yuburoll/KeeNoard/images/encoderFront.jpg

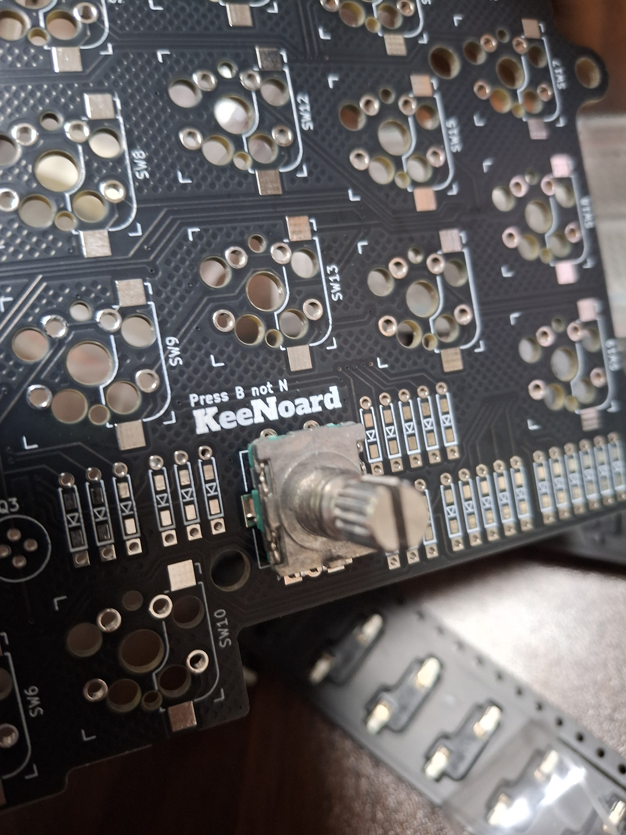
images/encoderFront.jpg
