yuburoll/KeeNoard/images/jumpers0.jpg

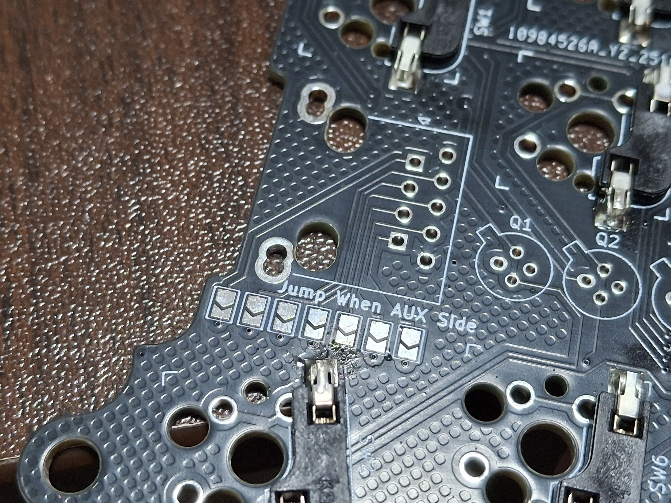
images/jumpers0.jpg
