yuburoll/KeeNoard/images/jumpers1.jpg

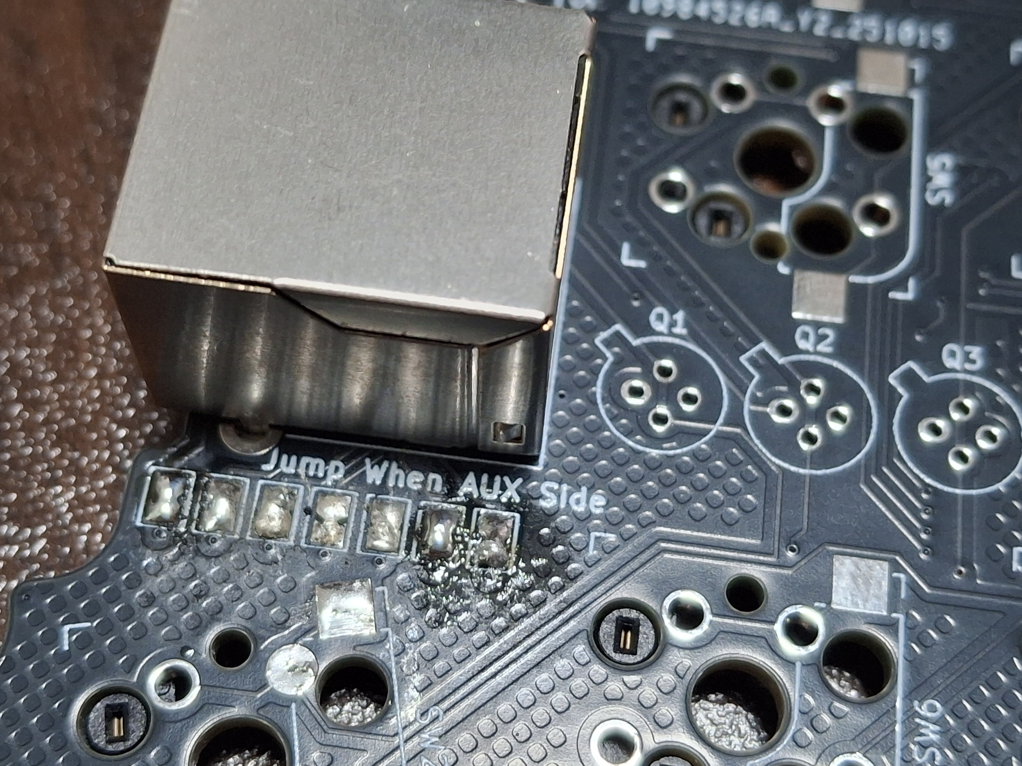
images/jumpers1.jpg
