yuburoll/KeeNoard/images/keenoardBoard.jpg

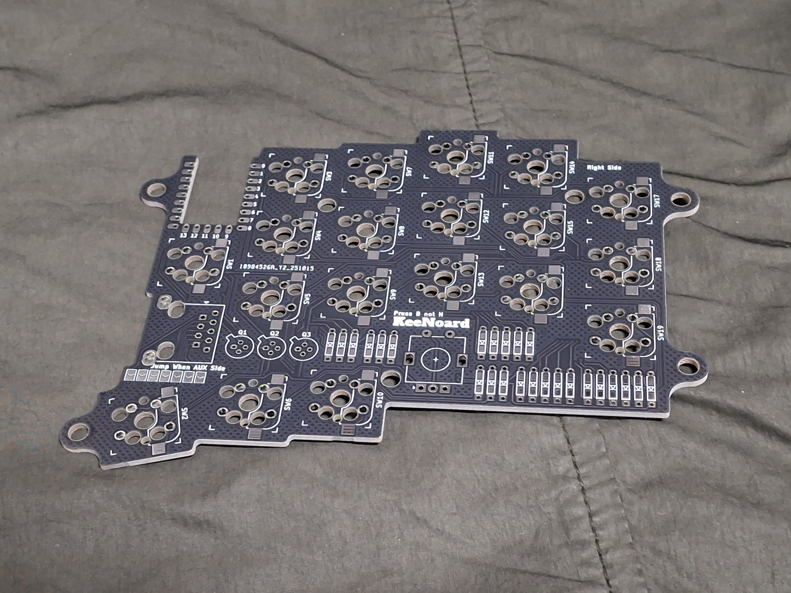
images/keenoardBoard.jpg
