yuburoll/KeeNoard/images/keenoardCaseV1.jpg

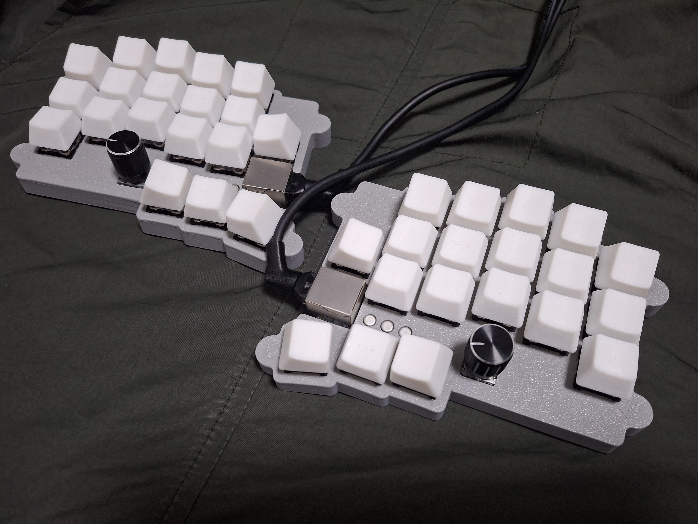
images/keenoardCaseV1.jpg
