yuburoll/KeeNoard/images/keenoardCaseV2.jpg

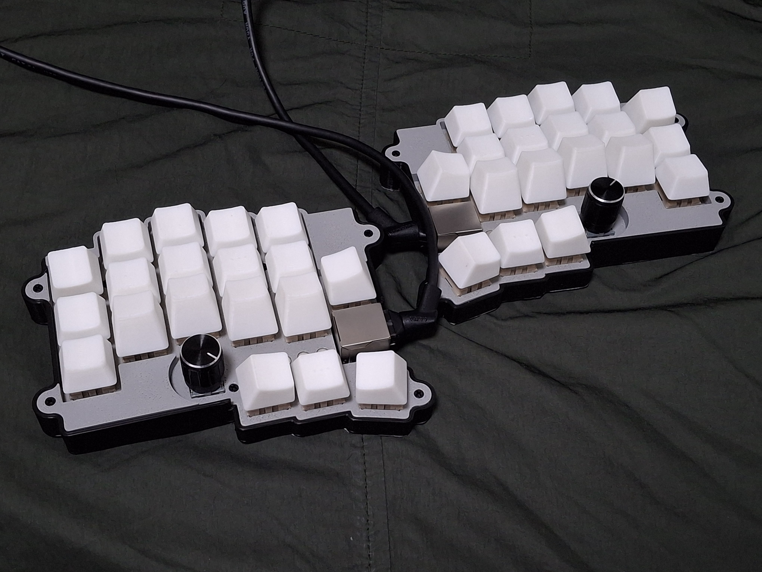
images/keenoardCaseV2.jpg
