yuburoll/KeeNoard/images/boardSolder0.jpg

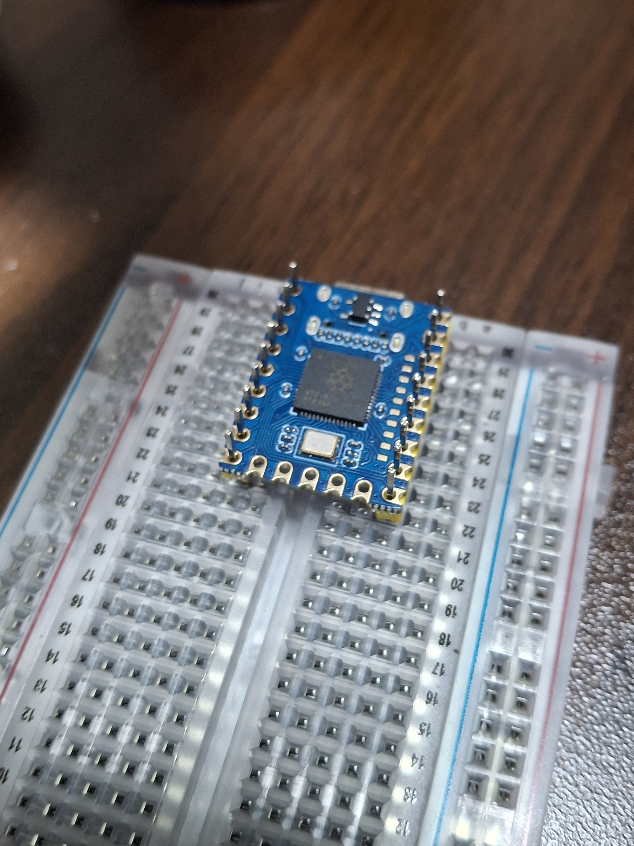
images/boardSolder0.jpg
