yuburoll/KeeNoard/images/boardSolder2.jpg

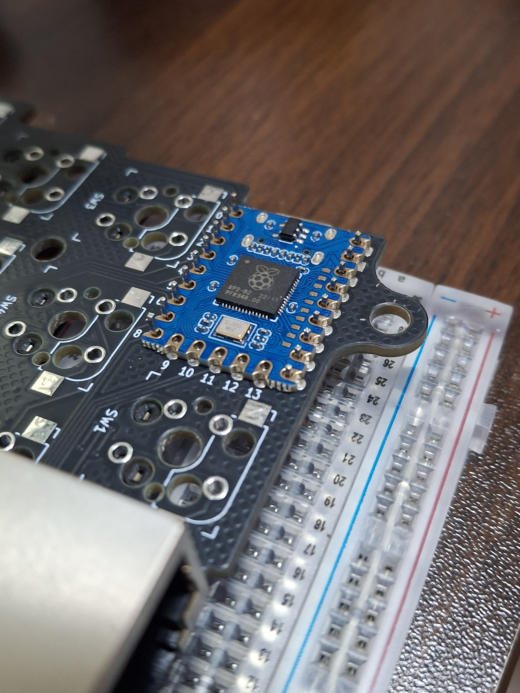
images/boardSolder2.jpg
