yuburoll/KeeNoard/images/caseV1Assembly0.jpg

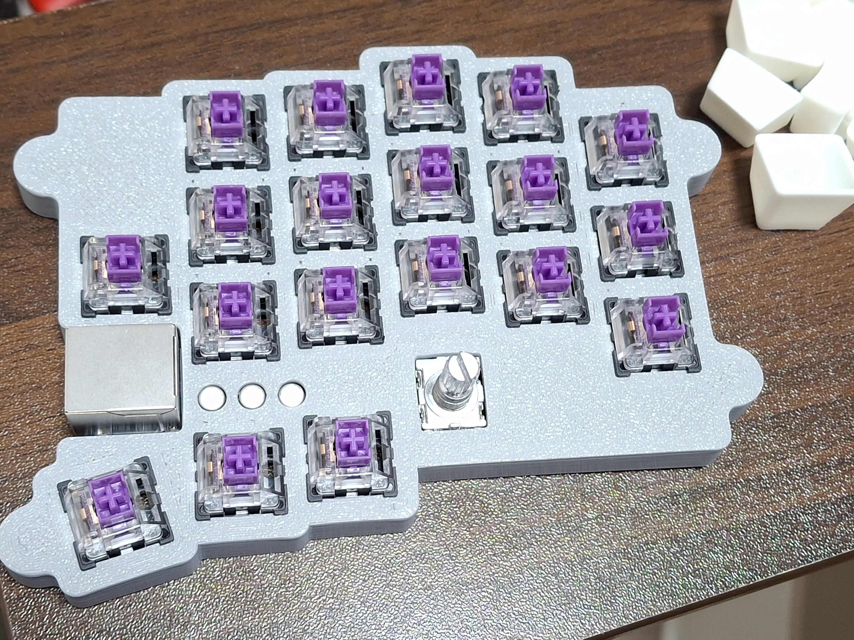
images/caseV1Assembly0.jpg
