yuburoll/KeeNoard/images/caseV1Assembly3.jpg

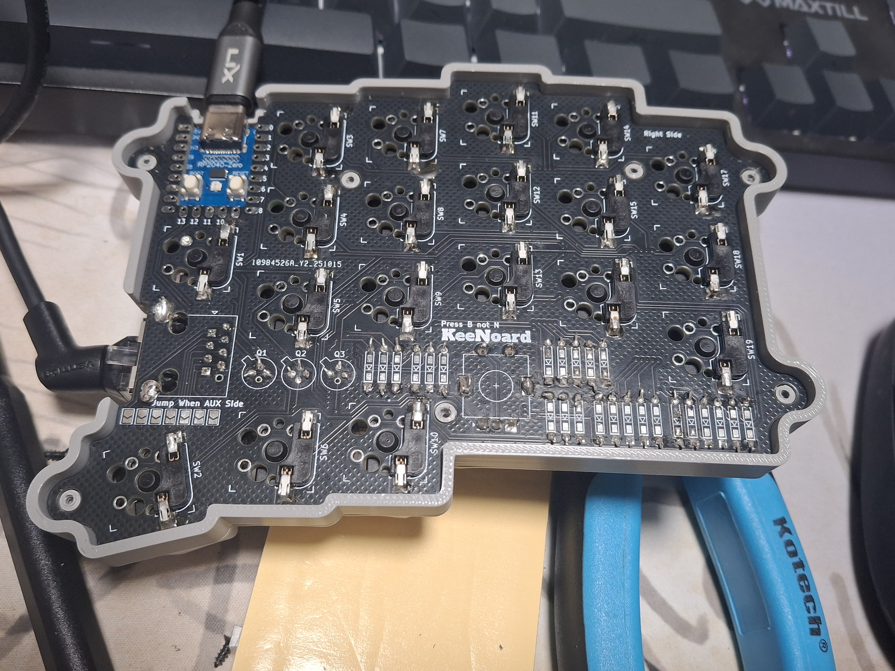
images/caseV1Assembly3.jpg
