yuburoll/KeeNoard/images/caseV2Assembly0.jpg

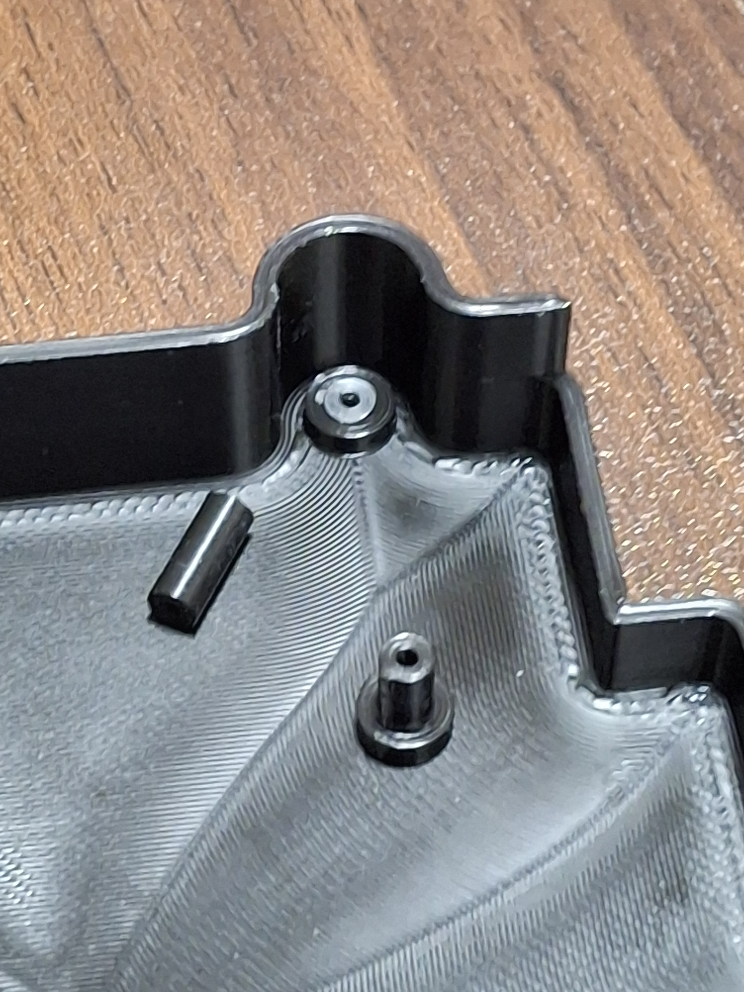
images/caseV2Assembly0.jpg
