yuburoll/KeeNoard/images/caseV2Assembly1.jpg

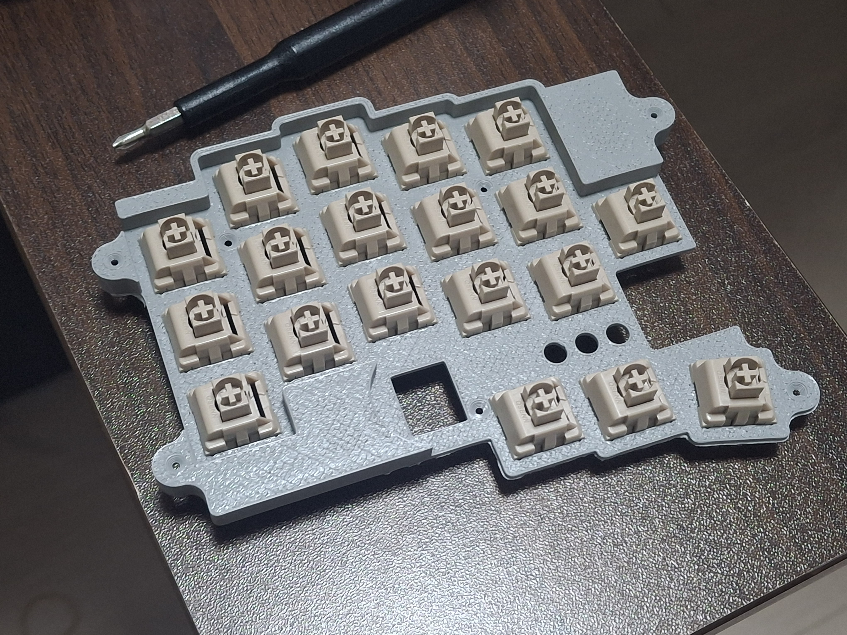
images/caseV2Assembly1.jpg
