yuburoll/KeeNoard/images/caseV2Assembly2.jpg

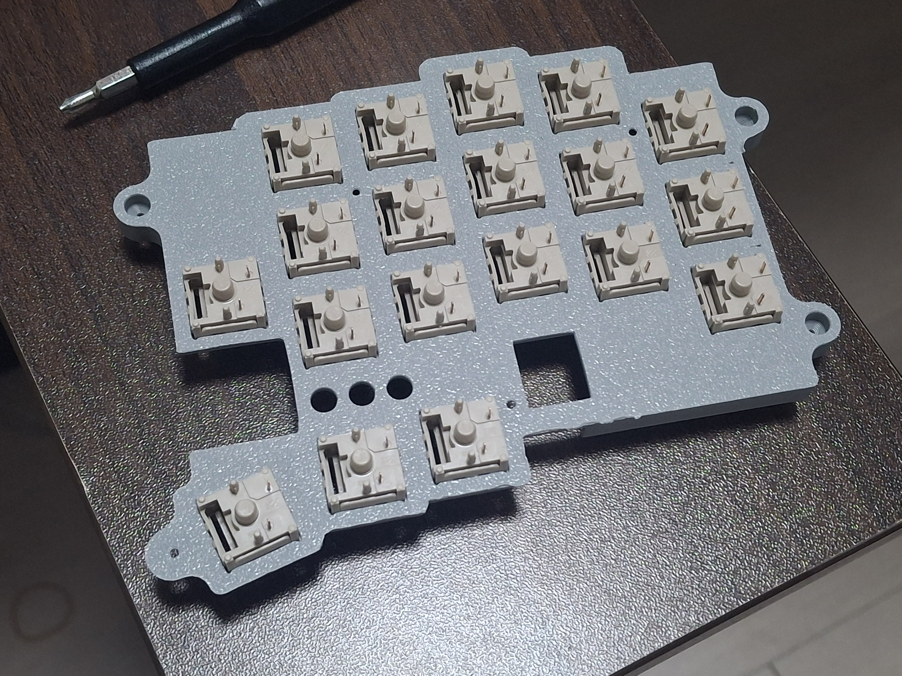
images/caseV2Assembly2.jpg
