yuburoll/KeeNoard/images/caseV2Assembly3.jpg

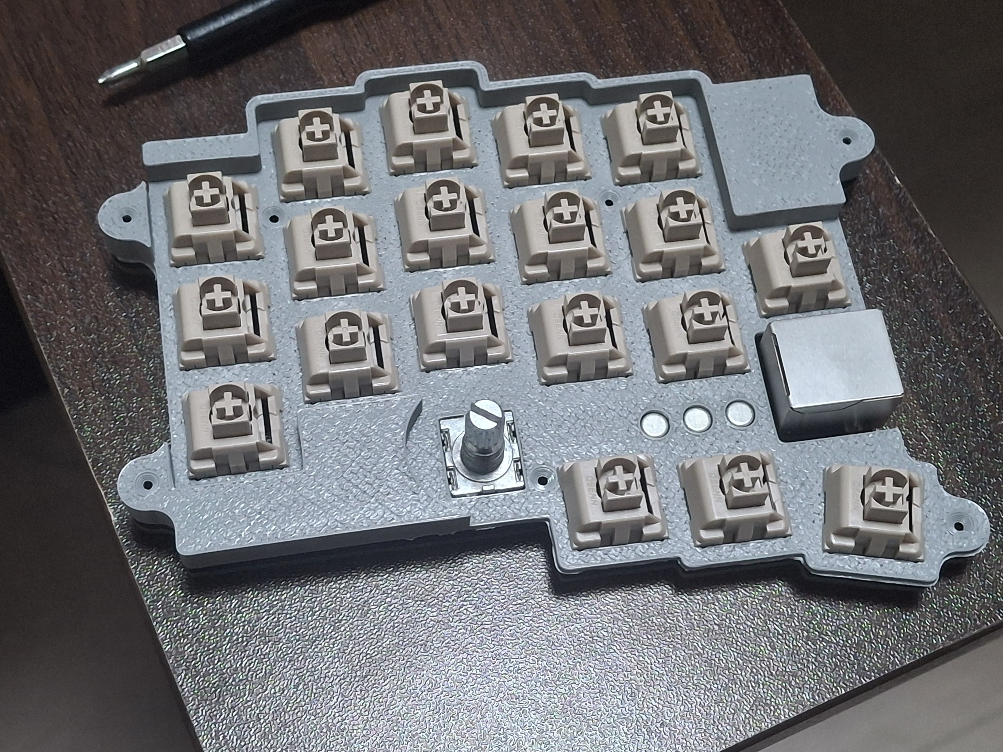
images/caseV2Assembly3.jpg
