yuburoll/KeeNoard/images/caseV2Assembly4.jpg

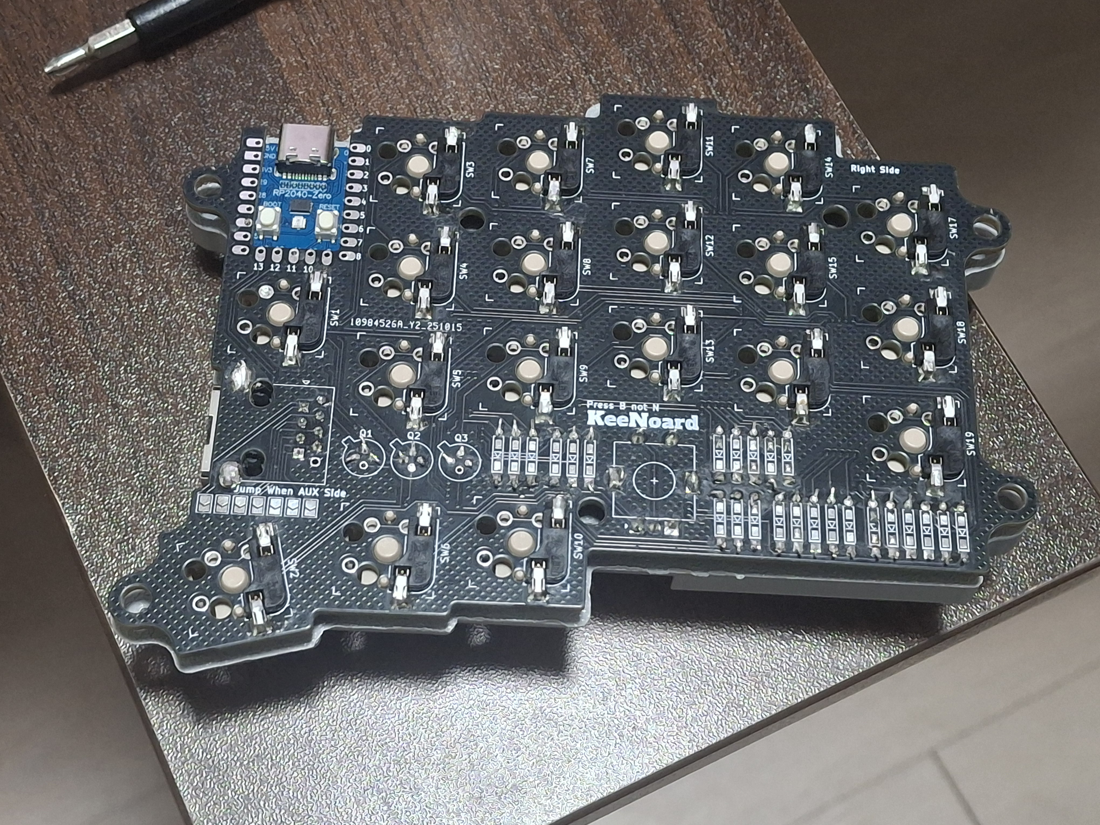
images/caseV2Assembly4.jpg
