yuburoll/KeeNoard/images/caseV2Assembly6.jpg

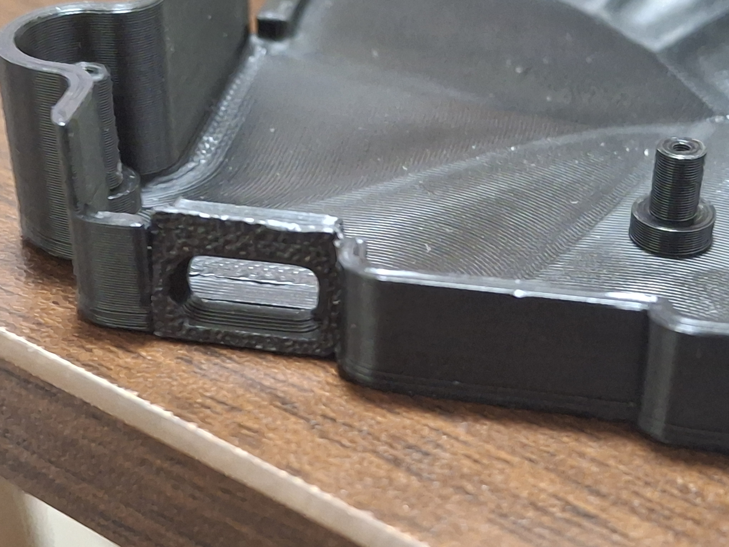
images/caseV2Assembly6.jpg
