yuburoll/KeeNoard/images/caseV2Assembly7.jpg

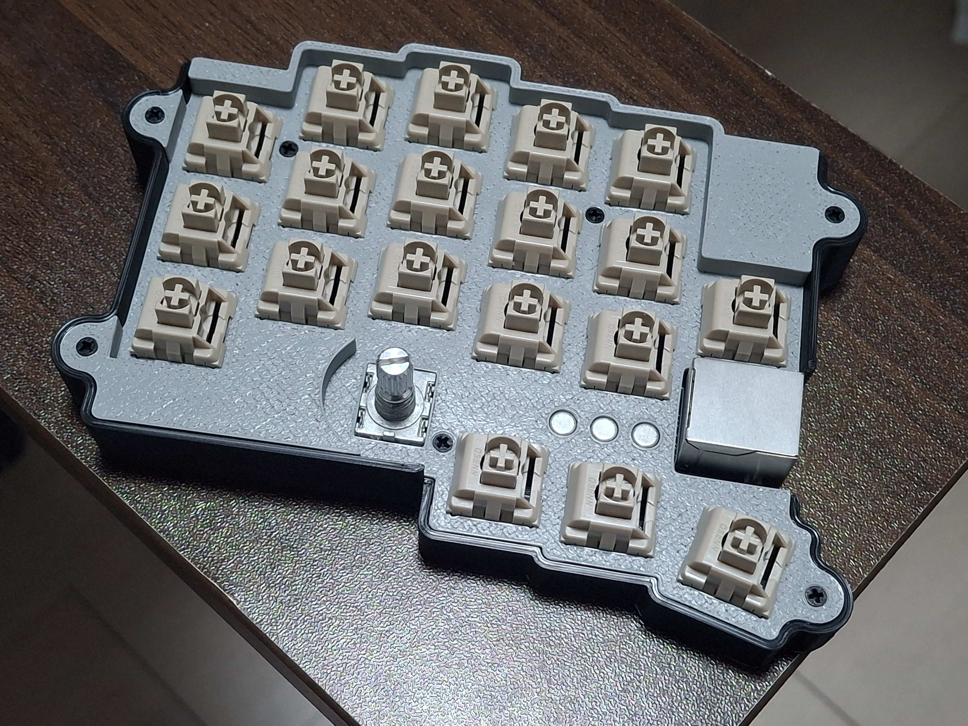
images/caseV2Assembly7.jpg
