yuburoll/KeeNoard/images/caseV2Assembly8.jpg

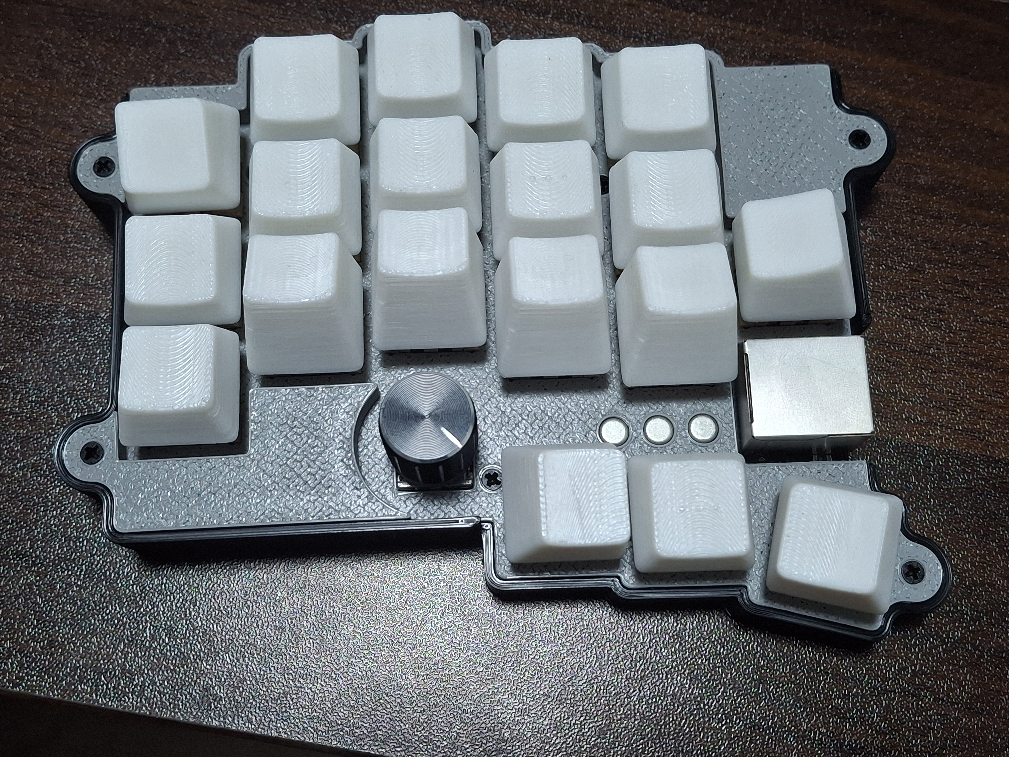
images/caseV2Assembly8.jpg
