yuburoll/KeeNoard/images/caseV3Assembly0.jpg

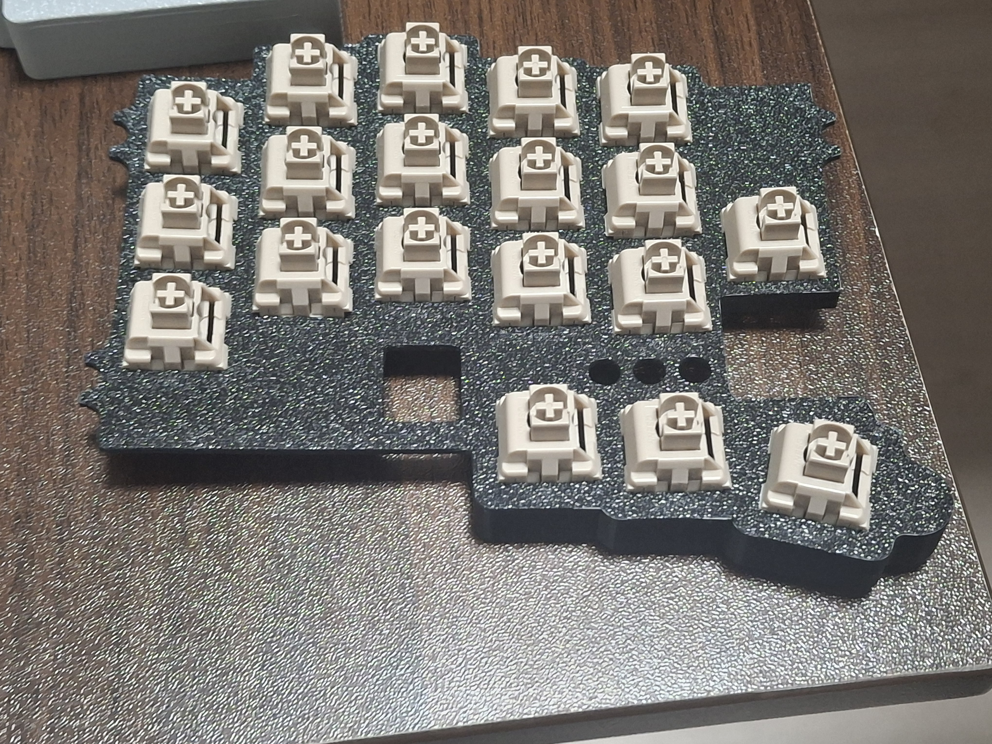
images/caseV3Assembly0.jpg
