yuburoll/KeeNoard/images/caseV3Assembly1.jpg

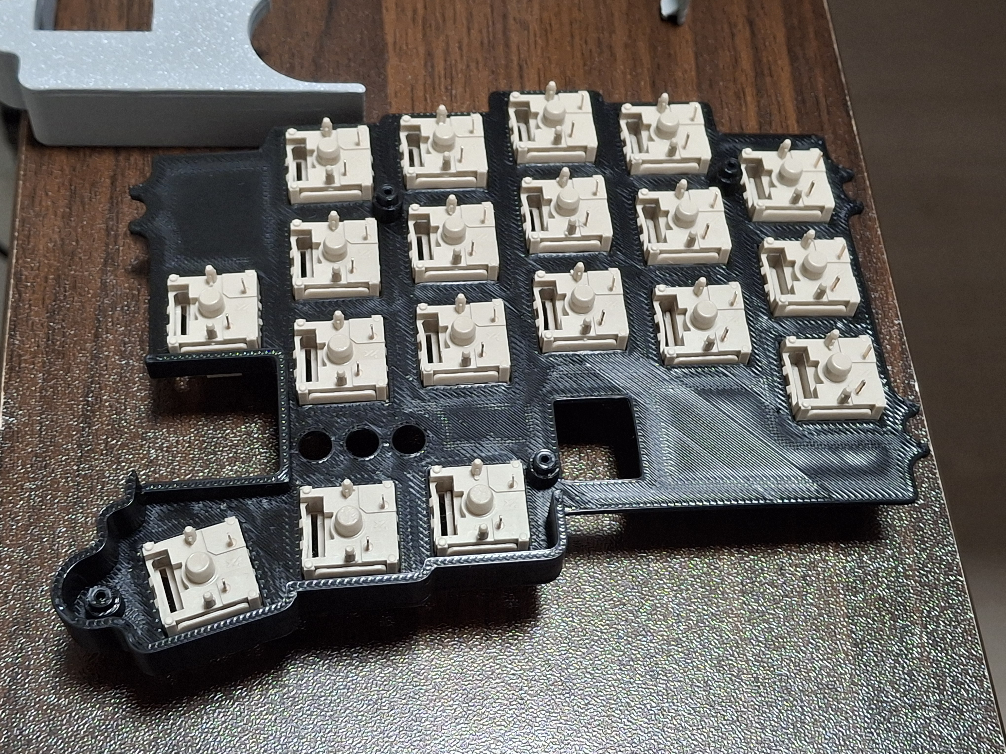
images/caseV3Assembly1.jpg
