yuburoll/KeeNoard/images/caseV3Assembly2.jpg

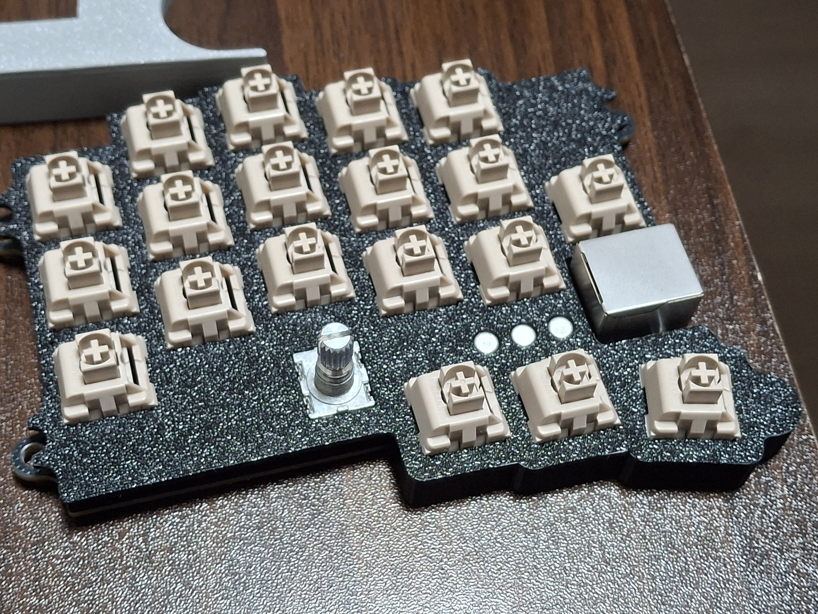
images/caseV3Assembly2.jpg
