yuburoll/KeeNoard/images/caseV3Assembly4.jpg

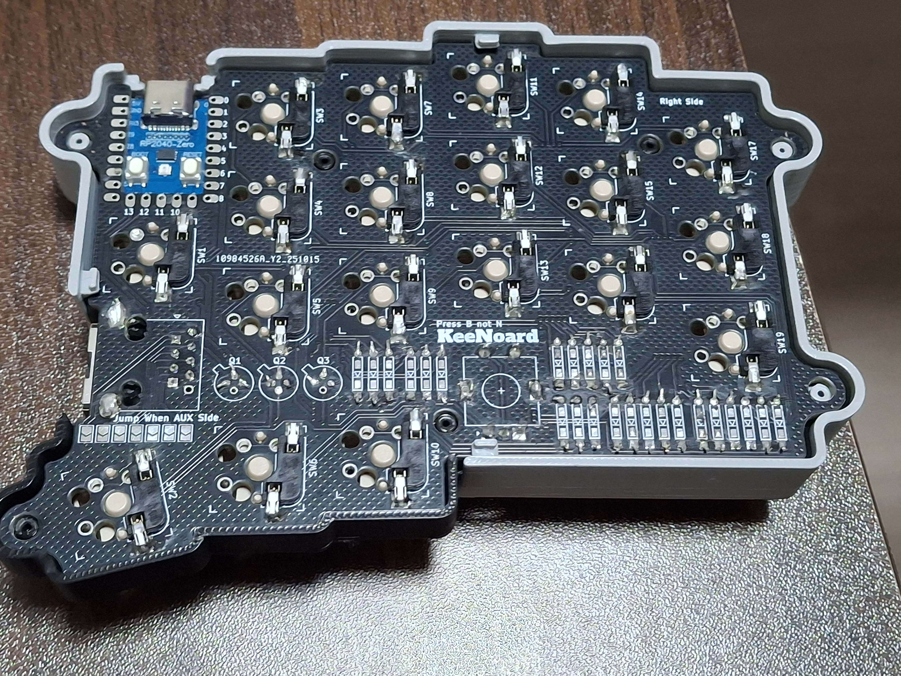
images/caseV3Assembly4.jpg
