yuburoll/KeeNoard/images/caseV3Assembly5.jpg

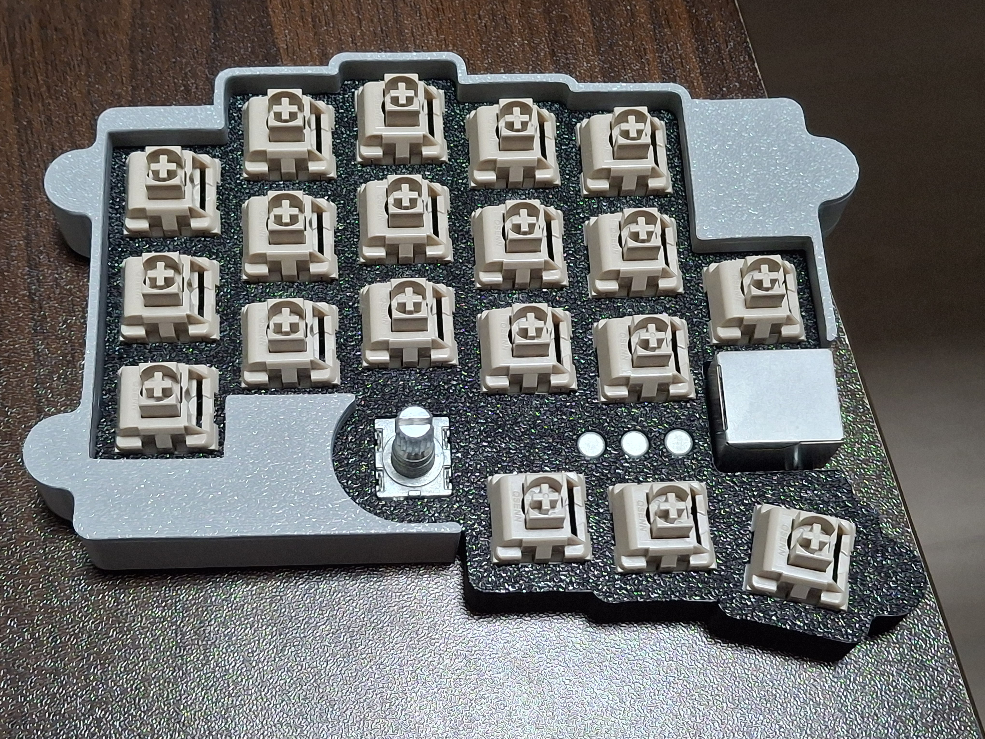
images/caseV3Assembly5.jpg
