yuburoll/KeeNoard/images/caseV3Assembly6.jpg

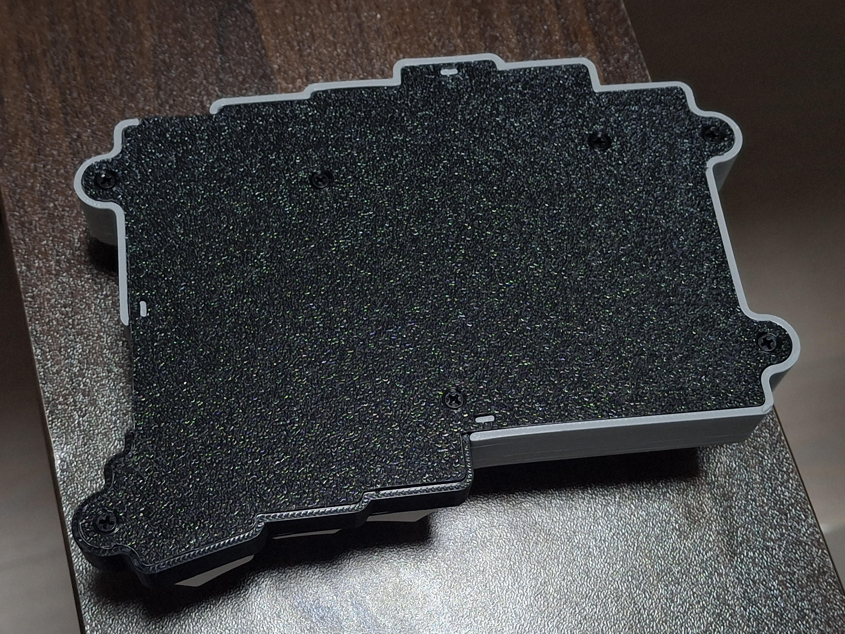
images/caseV3Assembly6.jpg
