yuburoll/KeeNoard/images/diodesSolder0.jpg

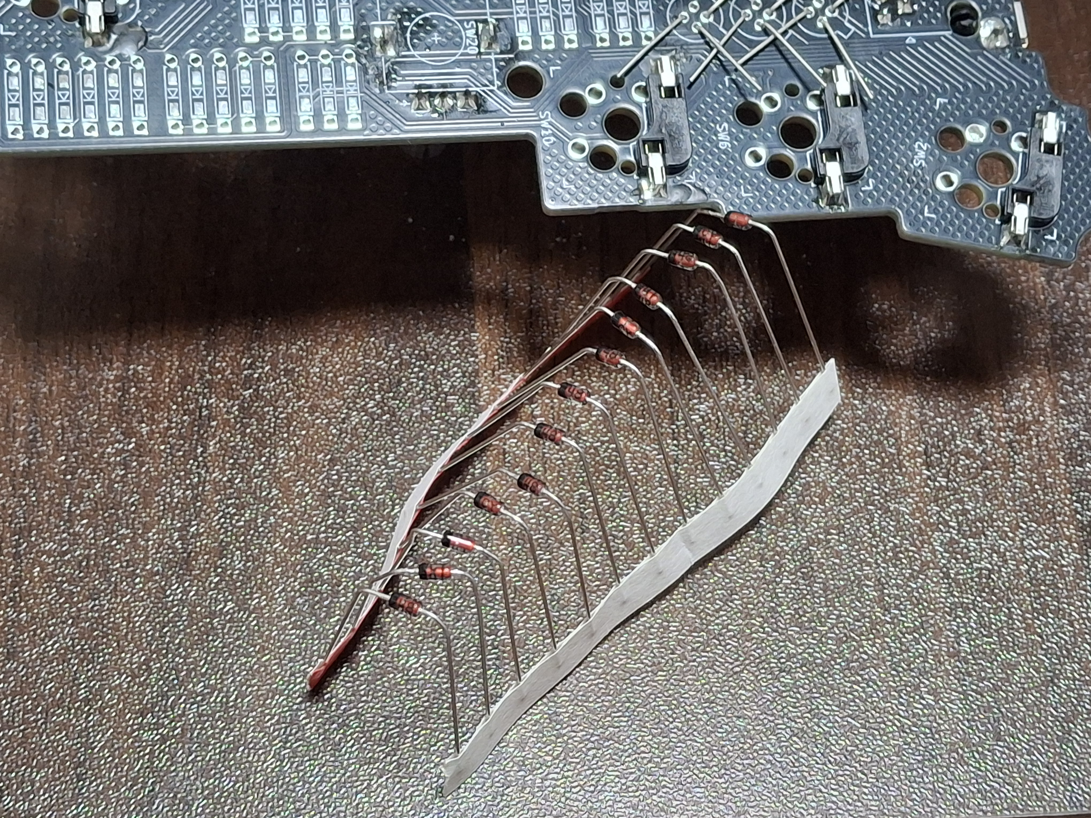
images/diodesSolder0.jpg
