yuburoll/KeeNoard/images/transistorSolder1.jpg

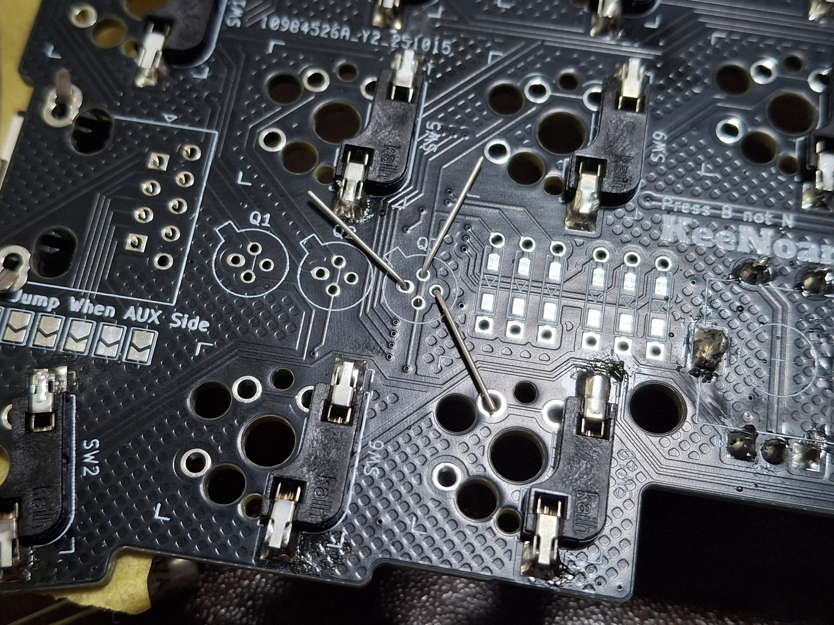
images/transistorSolder1.jpg
