yuburoll/KeeNoard/images/transistorSolder2.jpg

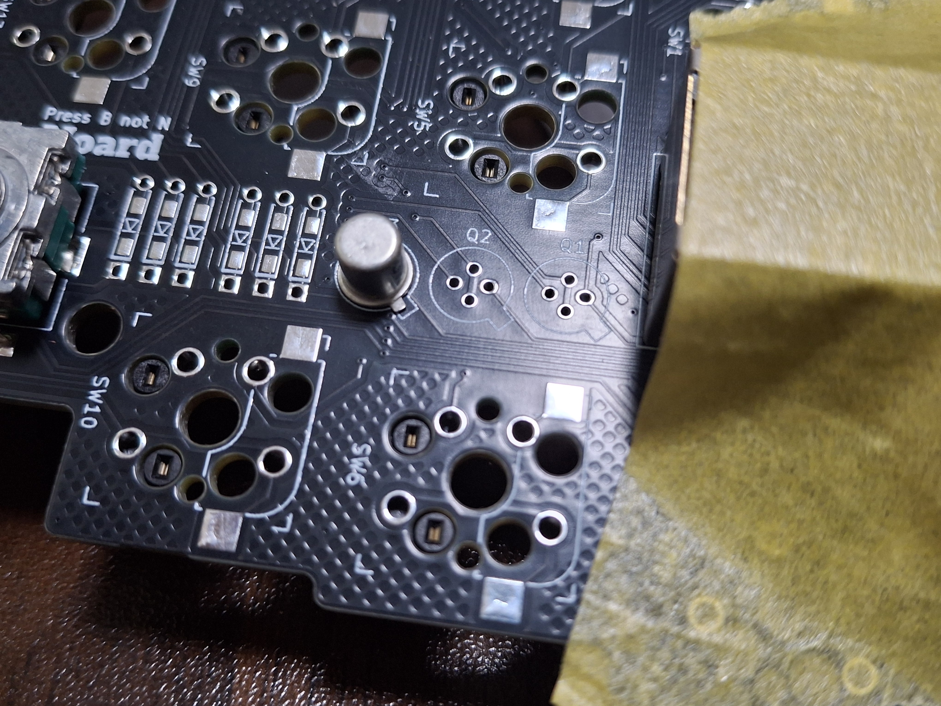
images/transistorSolder2.jpg
