yuburoll/KeeNoard/kicad/KeeNoard-SMD.kicad_sch

## KiCad design kicad/KeeNoard-SMD.kicad_sch (2025-10-31)

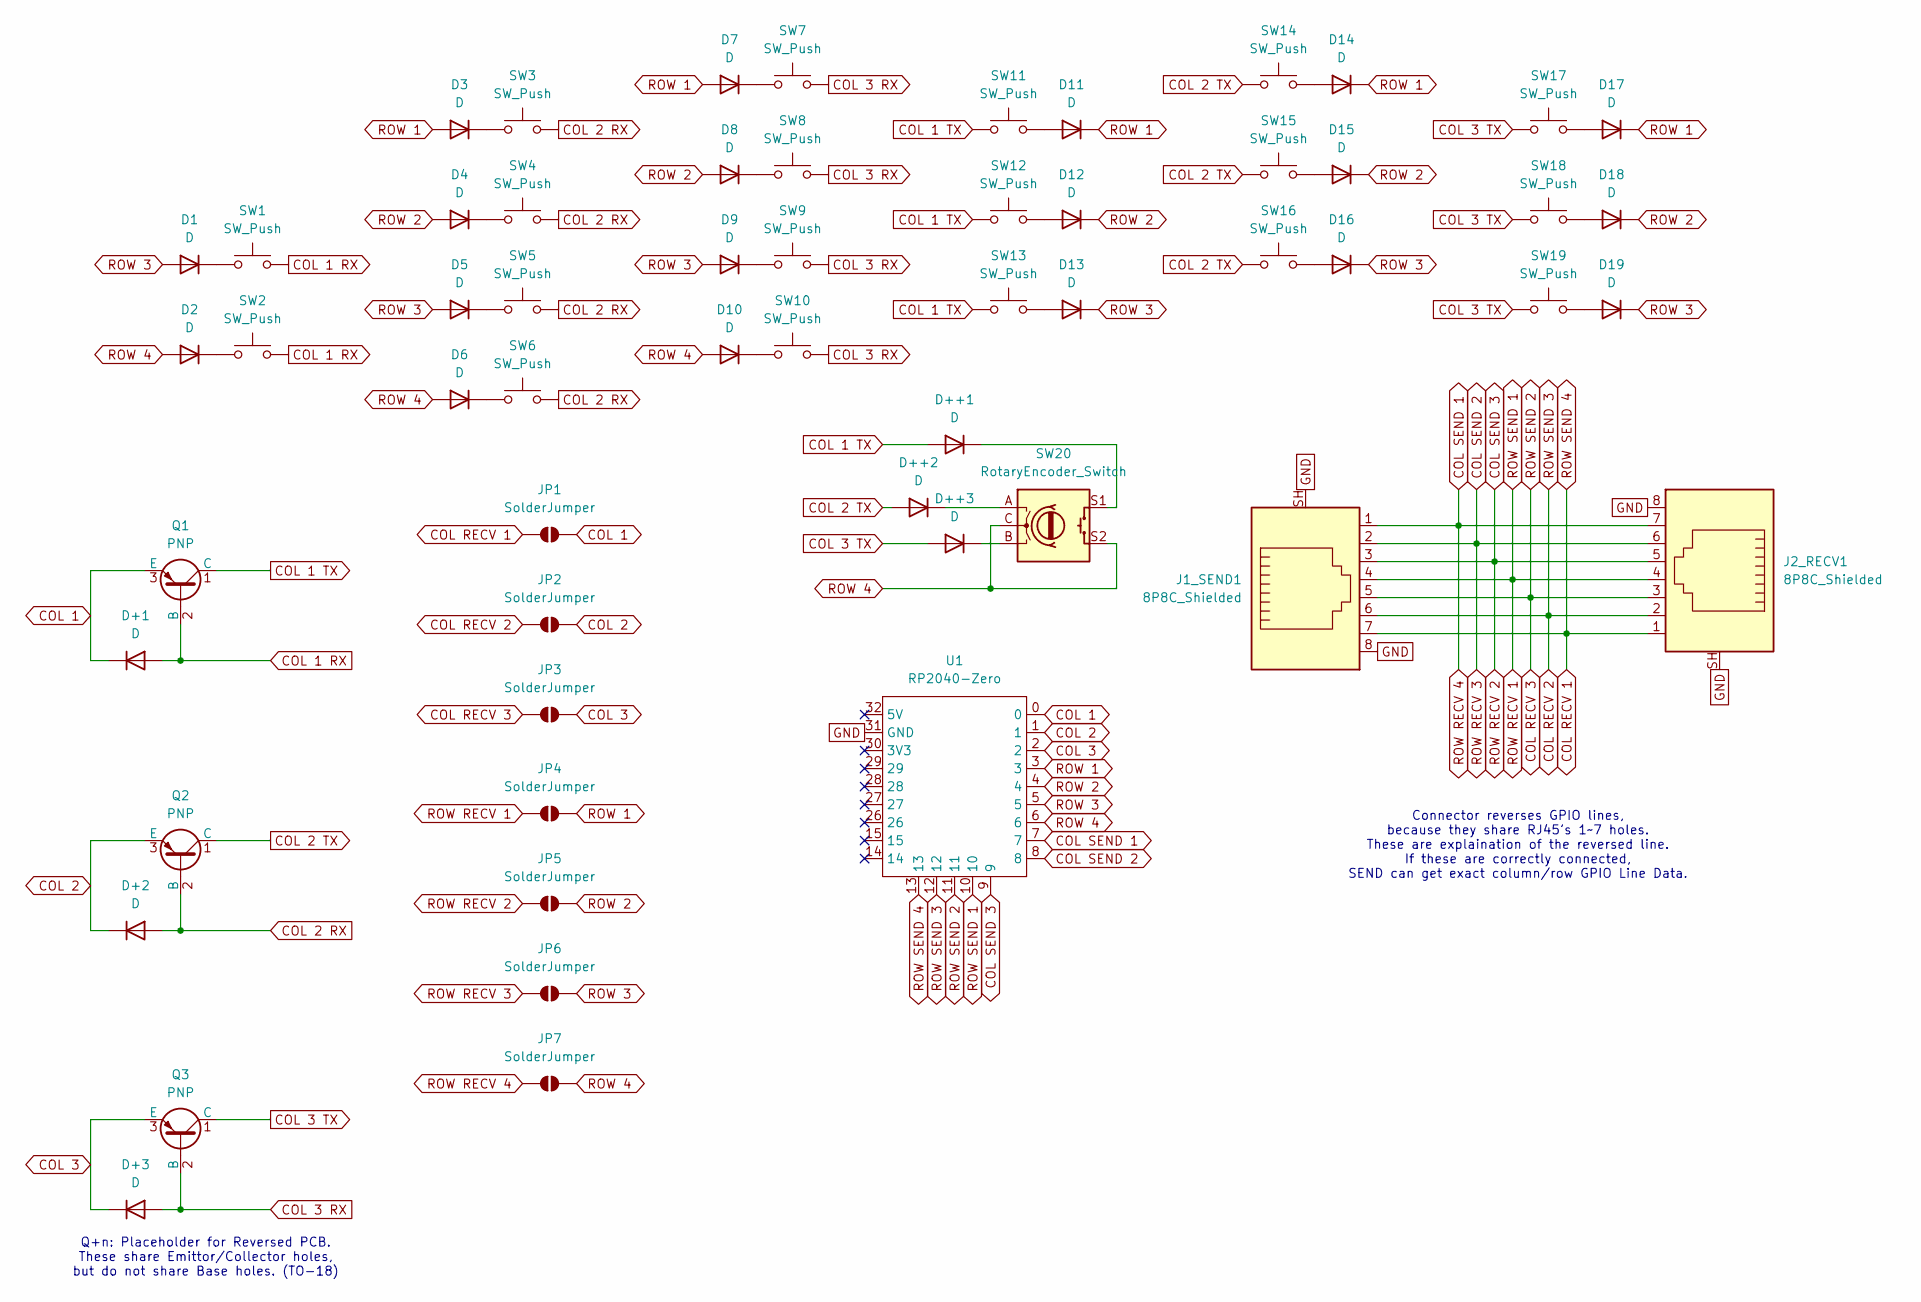
[picture p42: schematic KeeNoard-SMD.kicad_sch]

Parts:
D1, D2, D3, D4, D5, D6, D7, D8, D9, D10, D11, D12, D13, D14, D15, D16, D17, D18, D19: D
D+1, D+2, D+3: D
D++1, D++2, D++3: D
J1_SEND1, J2_RECV1: 8P8C_Shielded
JP1, JP2, JP3, JP4, JP5, JP6, JP7: SolderJumper
Q1, Q2, Q3: PNP
SW1, SW2, SW3, SW4, SW5, SW6, SW7, SW8, SW9, SW10, SW11, SW12, SW13, SW14, SW15, SW16, SW17, SW18, SW19: SW_Push
SW20: RotaryEncoder_Switch
U1: RP2040-Zero

Connections:
COL 1: D+1.1 (K), JP1.2 (B), Q1.3 (E), U1.0
COL 1 RX: D+1.2 (A), Q1.2 (B), SW1.1, SW2.1
COL 1 TX: D++1.2 (A), Q1.1 (C), SW11.2, SW12.2, SW13.2
COL 2: D+2.1 (K), JP2.2 (B), Q2.3 (E), U1.1
COL 2 RX: D+2.2 (A), Q2.2 (B), SW3.1, SW4.1, SW5.1, SW6.1
COL 2 TX: D++2.2 (A), Q2.1 (C), SW14.2, SW15.2, SW16.2
COL 3: D+3.1 (K), JP3.2 (B), Q3.3 (E), U1.2
COL 3 RX: D+3.2 (A), Q3.2 (B), SW7.1, SW8.1, SW9.1, SW10.1
COL 3 TX: D++3.2 (A), Q3.1 (C), SW17.2, SW18.2, SW19.2
COL RECV 1: J1_SEND1.7, J2_RECV1.1, JP1.1 (A), U1.13
COL RECV 2: J1_SEND1.6, J2_RECV1.2, JP2.1 (A), U1.12
COL RECV 3: J1_SEND1.5, J2_RECV1.3, JP3.1 (A), U1.11
COL SEND 1: J1_SEND1.1, J2_RECV1.7, JP7.1 (A), U1.7
COL SEND 2: J1_SEND1.2, J2_RECV1.6, JP6.1 (A), U1.8
COL SEND 3: J1_SEND1.3, J2_RECV1.5, JP5.1 (A), U1.9
GND: J1_SEND1.8, J1_SEND1.SH, J2_RECV1.8, J2_RECV1.SH, U1.31 (GND)
unnamed: D1.1 (K), SW1.2
unnamed: D2.1 (K), SW2.2
unnamed: D3.1 (K), SW3.2
unnamed: D4.1 (K), SW4.2
unnamed: D5.1 (K), SW5.2
unnamed: D6.1 (K), SW6.2
unnamed: D7.1 (K), SW7.2
unnamed: D8.1 (K), SW8.2
unnamed: D9.1 (K), SW9.2
unnamed: D10.1 (K), SW10.2
unnamed: D11.2 (A), SW11.1
unnamed: D12.2 (A), SW12.1
unnamed: D13.2 (A), SW13.1
unnamed: D14.2 (A), SW14.1
unnamed: D15.2 (A), SW15.1
unnamed: D16.2 (A), SW16.1
unnamed: D17.2 (A), SW17.1
unnamed: D18.2 (A), SW18.1
unnamed: D19.2 (A), SW19.1
unnamed: D++1.1 (K), SW20.S1
unnamed: D++2.1 (K), SW20.A
unnamed: D++3.1 (K), SW20.B
ROW 1: D3.2 (A), D7.2 (A), D11.1 (K), D14.1 (K), D17.1 (K), JP4.2 (B), U1.3
ROW 2: D4.2 (A), D8.2 (A), D12.1 (K), D15.1 (K), D18.1 (K), JP5.2 (B), U1.4
ROW 3: D1.2 (A), D5.2 (A), D9.2 (A), D13.1 (K), D16.1 (K), D19.1 (K), JP6.2 (B), U1.5
ROW 4: D2.2 (A), D6.2 (A), D10.2 (A), JP7.2 (B), SW20.C, SW20.S2, U1.6
ROW RECV 1: J1_SEND1.4, J2_RECV1.4, JP4.1 (A), U1.10

Notes on the sheet:
Connector reverses GPIO lines, because they share RJ45's 1~7 holes. These are explaination of the reversed line. If these are correctly connected, SEND can get exact column/row GPIO Line Data.
Q+n: Placeholder for Reversed PCB. These share Emittor/Collector holes, but do not share Base holes. (TO-18)
