yuburoll/KeeNoard/firmware/keenoard/keymaps/leftboard_vial/config.h

/* SPDX-License-Identifier: GPL-2.0-or-later */

#pragma once

#undef DYNAMIC_KEYMAP_LAYER_COUNT
#define DYNAMIC_KEYMAP_LAYER_COUNT 8

#define VIAL_KEYBOARD_UID {0x66, 0xC4, 0x7E, 0x92, 0x1A, 0x32, 0xAD, 0xF5}
#define VIAL_UNLOCK_COMBO_ROWS { 2, 6 }
#define VIAL_UNLOCK_COMBO_COLS { 5, 11 }
