yuburoll/KeeNoard/firmware/keenoard/matrix.c

/*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
Copied from here: https://github.com/e3w2q/qmk_firmware/blob/762fe3e0a7cbea768245a75520f06ff5a2f00b9f/keyboards/2x3test/matrix.c
*/

/*
created by Yuburoll
edited from cheapino's matrix.c by Thomas Haukland
can be checked from here: https://github.com/tompi/qmk_firmware/blob/cheapinov2-miryoku/keyboards/cheapino/matrix.c

edited matrix to active high, and edited encoder
*/

/*
 * scan matrix
 */
#include <stdint.h>
#include <stdbool.h>
#include "wait.h"
#include "util.h"
#include "matrix.h"
#include "config.h"
#include "quantum.h"
#include "debounce.h"
#include "encoder.h"
#include "print.h"

#define MATRIX_IO_READ_DELAY 15
#define MATRIX_IO_CLEAR_DELAY 15

#define COL_SHIFTER ((uint16_t)1)

static const pin_t row_pins[] = MATRIX_ROW_PINS;
static const pin_t col_pins[] = MATRIX_COL_PINS;
static matrix_row_t previous_matrix[MATRIX_ROWS];

static void select_row(uint8_t row) {
    setPinOutputPushPull(row_pins[row]);
    writePinHigh(row_pins[row]);
}

static void unselect_row(uint8_t row) {
    setPinInputLow(row_pins[row]);
}

static void unselect_rows(void) {
    for (uint8_t x = 0; x < MATRIX_ROWS; x++) {
        setPinInputLow(row_pins[x]);
    }
}

static void select_col(uint8_t col) {
    setPinOutputPushPull(col_pins[col]);
    writePinHigh(col_pins[col]);
}

static void unselect_col(uint8_t col) {
    setPinInputLow(col_pins[col]);
}

static void unselect_cols(void) {
    for (uint8_t x = 0; x < MATRIX_COLS/2; x++) {
        setPinInputLow(col_pins[x*2]);
    }
}

static void read_cols_on_row(matrix_row_t current_matrix[], uint8_t current_row) {
    // Select row and wait for row selection to stabilize
    select_row(current_row);
    wait_us(MATRIX_IO_READ_DELAY);

    // For each col...
    for (uint8_t col_index = 0; col_index < MATRIX_COLS / 2; col_index++) {
        uint16_t column_index_bitmask = COL_SHIFTER << ((col_index * 2));
        // Check row pin state
        if (!readPin(col_pins[col_index*2])) {
            // Pin HI, clear col bit
            current_matrix[current_row] &= ~column_index_bitmask;
        } else {
            // Pin LO, set col bit
            current_matrix[current_row] |= column_index_bitmask;
        }
    }

    // Unselect row, clear
    unselect_row(current_row);
    wait_us(MATRIX_IO_CLEAR_DELAY);
}

static void read_rows_on_col(matrix_row_t current_matrix[], uint8_t current_col) {
    // Select col and wait for col selection to stabilize
    select_col(current_col*2);
    wait_us(MATRIX_IO_READ_DELAY);

    uint16_t column_index_bitmask = COL_SHIFTER << ((current_col * 2)+1);
    // For each row...
    for (uint8_t row_index = 0; row_index < MATRIX_ROWS; row_index++) {
        // Check row pin state
        if (!readPin(row_pins[row_index])) {
            // Pin HI, clear col bit
            current_matrix[row_index] &= ~column_index_bitmask;
        } else {
            // Pin LO, set col bit
            current_matrix[row_index] |= column_index_bitmask;
        }
    }
    // Unselect col, clear
    unselect_col(current_col*2);
    wait_us(MATRIX_IO_CLEAR_DELAY);
}


void matrix_init_custom(void) {
    // initialize key pins
    unselect_cols();
    unselect_rows();
    debounce_init(MATRIX_ROWS);
}

void store_old_matrix(matrix_row_t current_matrix[]) {
    for (uint8_t i = 0; i < MATRIX_ROWS; i++) {
        previous_matrix[i] = current_matrix[i];
    }
}

bool has_matrix_changed(matrix_row_t current_matrix[]) {
    for (uint8_t i = 0; i < MATRIX_ROWS; i++) {
        if (previous_matrix[i] != current_matrix[i]) return true;
    }
    return false;
}

bool matrix_scan_custom(matrix_row_t current_matrix[]) {
    
    store_old_matrix(current_matrix);
    // Set row, read cols
    for (uint8_t current_row = 0; current_row < MATRIX_ROWS; current_row++) {
        read_cols_on_row(current_matrix, current_row);
    }
    // Set col, read rows
    for (uint8_t current_col = 0; current_col < MATRIX_COLS/2; current_col++) {
        read_rows_on_col(current_matrix, current_col);
    }

    #ifdef ENCODER_ENABLE
    custom_encoder_action(current_matrix);
    #endif
    
    return has_matrix_changed(current_matrix);
}
