yuburoll/KeeNoard/images/encoderBack.jpg

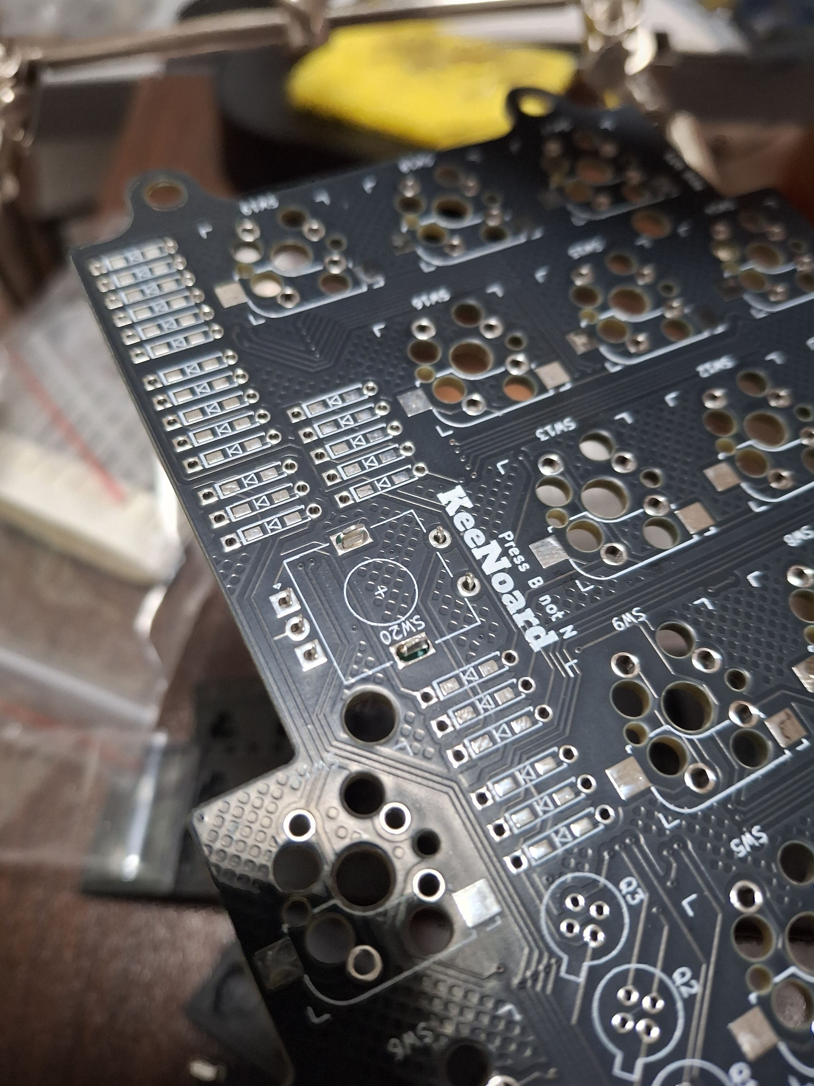
images/encoderBack.jpg
