yuburoll/KeeNoard/images/hotswapWarn.jpg

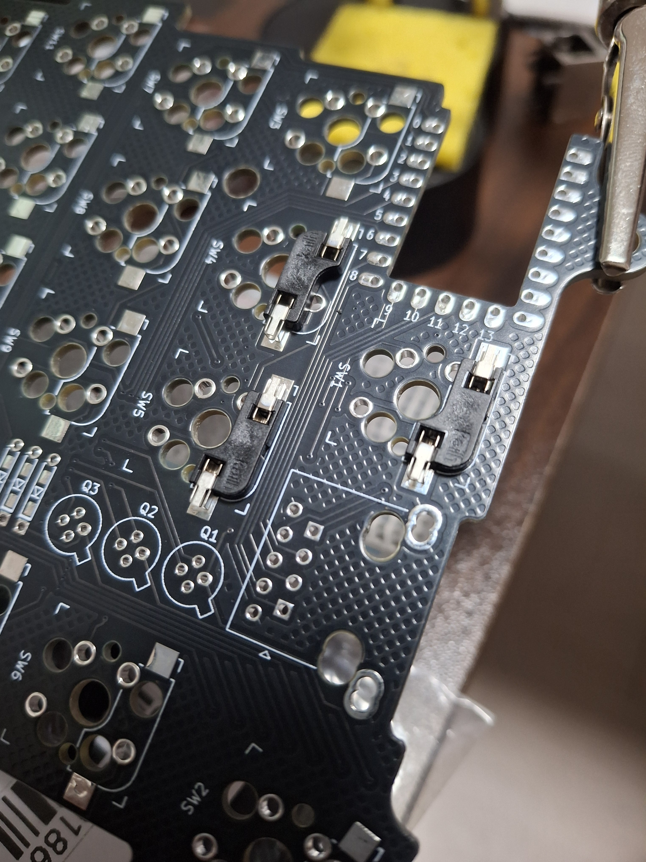
images/hotswapWarn.jpg
