yuburoll/KeeNoard/images/boardSolder1.jpg

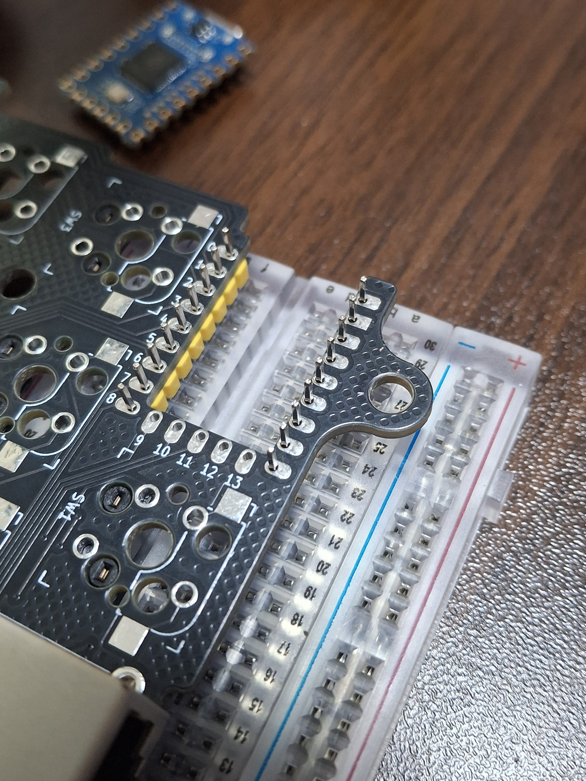
images/boardSolder1.jpg
